HMS-RIC/EMG-EEG-Amplifier/Photos/_1160738.JPG

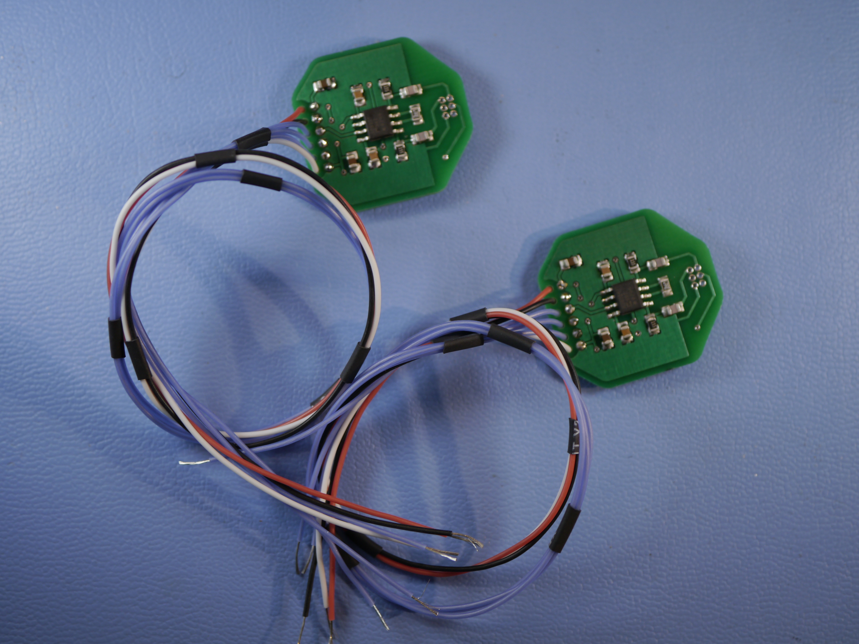
Photos/_1160738.JPG
