HMS-RIC/EMG-EEG-Amplifier/Photos/_1160741.JPG

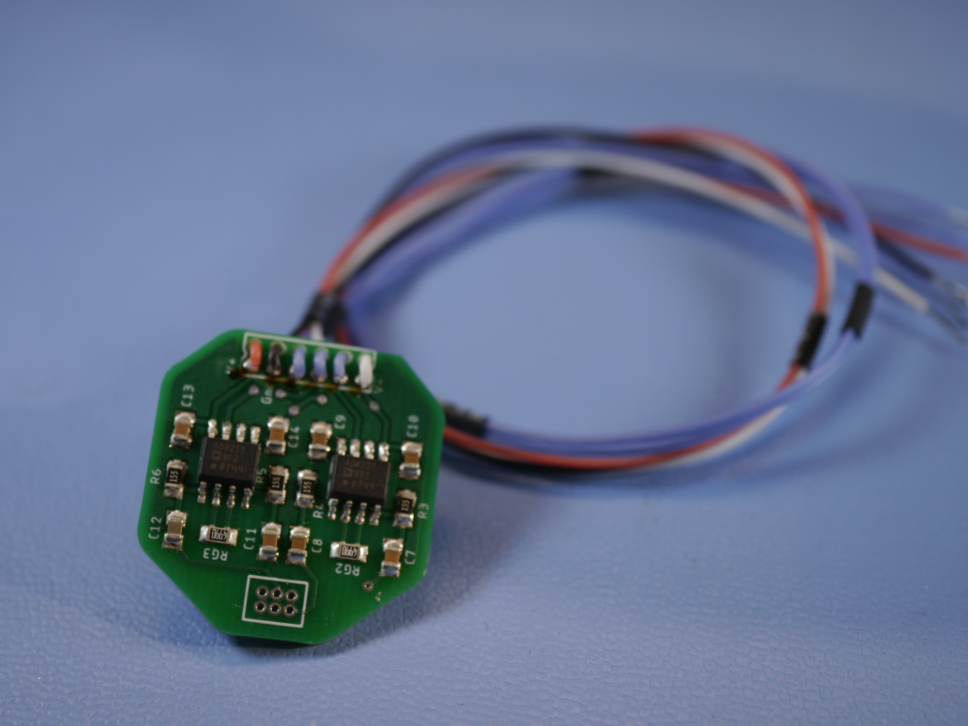
Photos/_1160741.JPG
