HMS-RIC/EMG-EEG-Amplifier/Photos/_1160742.JPG

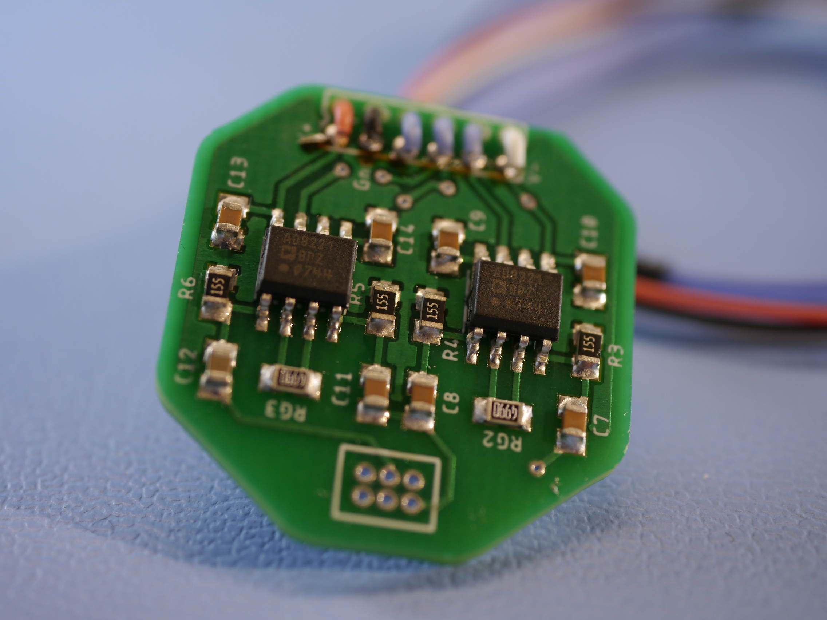
Photos/_1160742.JPG
