HMS-RIC/EMG-EEG-Amplifier/EEG_EMG_InAMP.asc

C1: cap; 10e-9
C2: cap; 10e-9
C3: cap; .1e-6
C4: cap; 10e-6
C5: cap; .1e-6
C6: cap; 10e-6
C7: cap; .1e-6
C8: cap; .1e-6
C9: cap; .1e-6
C10: cap; 10e-6
C11: cap; .1e-6
C12: cap; 10e-6
C13: cap; .1e-6
C14: cap; 10e-6
C15: cap; .1e-6
C16: cap; 10e-6
C17: cap; .1e-6
C18: cap; .1e-6
R1: res; 499; tol=.1 pwr=.25
R2: res; 1.5e6
R3: res; 1.5e6
R4: res; 499; tol=.1 pwr=.25
R5: res; 3e6
R6: res; 3e6
R7: res; 499; tol=.1 pwr=.25
R8: res; 3e6
R9: res; 3e6
U1: AD8221
U2: AD8221
U3: AD8221
V1: voltage; 15
V2: voltage; 15
V3: voltage; SINE(0 12 5)
V4: voltage; SINE(0 .05 100 0 0 360); AC 1
V5: voltage; SINE(0 .05 100 0 0 0); AC 1
V6: voltage; SINE(0 5 60)
V8: voltage; SINE(0 .05 .5 0 0 0); AC .05
V9: voltage; SINE(0 .05 10 0 0 360); AC .05
Named nets: 0, +VS, -VS, OUT1, OUT2, OUT3
.ac dec 10 .01 1000
